MRRP-lab/ripple_robot/cad/fea/out/quasi-static_reaction_force.gif

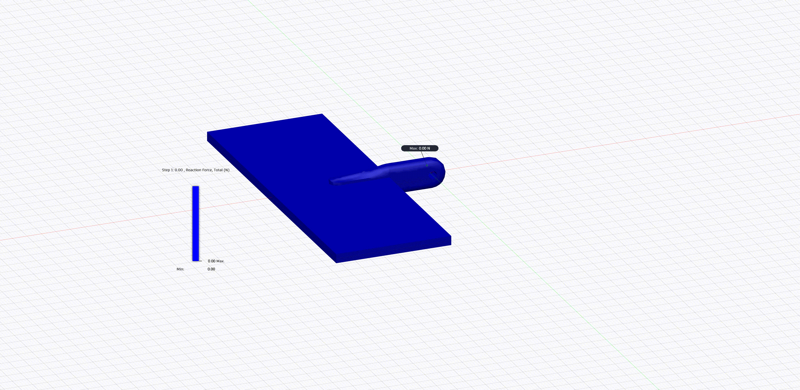
cad/fea/out/quasi-static_reaction_force.gif
