MRRP-lab/ripple_robot/cad/fea/out/quasi-static_stress.gif

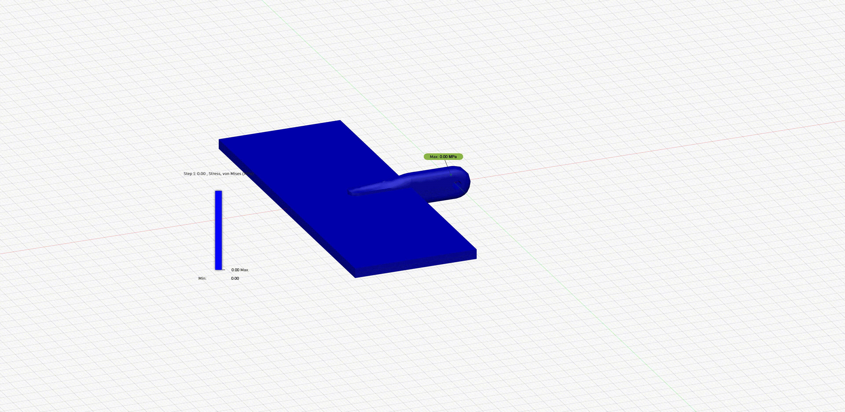
cad/fea/out/quasi-static_stress.gif
