MRRP-lab/ripple_robot/cad/fea/out/quasi-static_stress_cropped.gif

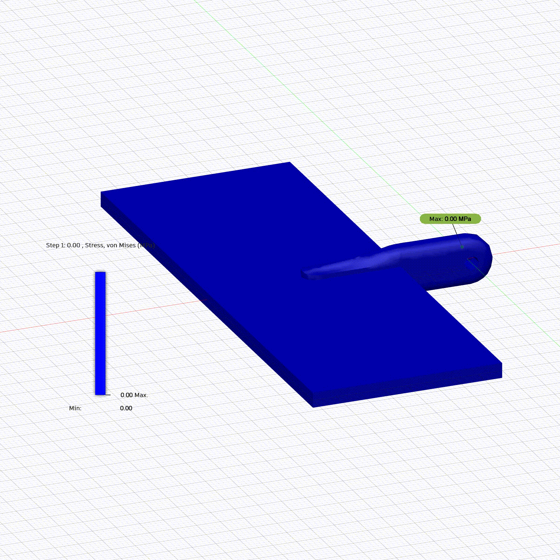
cad/fea/out/quasi-static_stress_cropped.gif
