MRRP-lab/ripple_robot/cad/fea/out/reaction_force_40deg.png

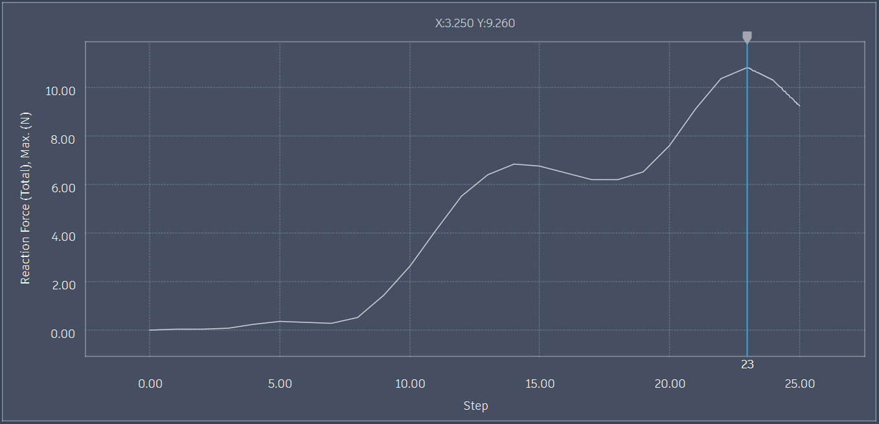
cad/fea/out/reaction_force_40deg.png
