MRRP-lab/ripple_robot/scripts/out/gait_stability.gif

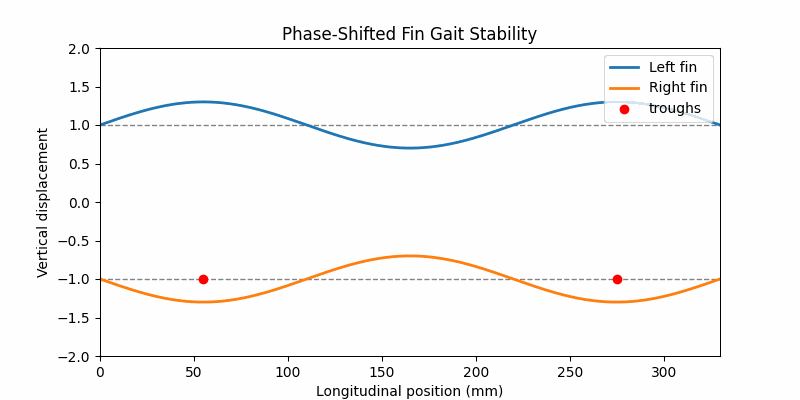
scripts/out/gait_stability.gif
