MRRP-lab/ripple_robot/cad/v4/stls/10p_passthrough_profile.stl

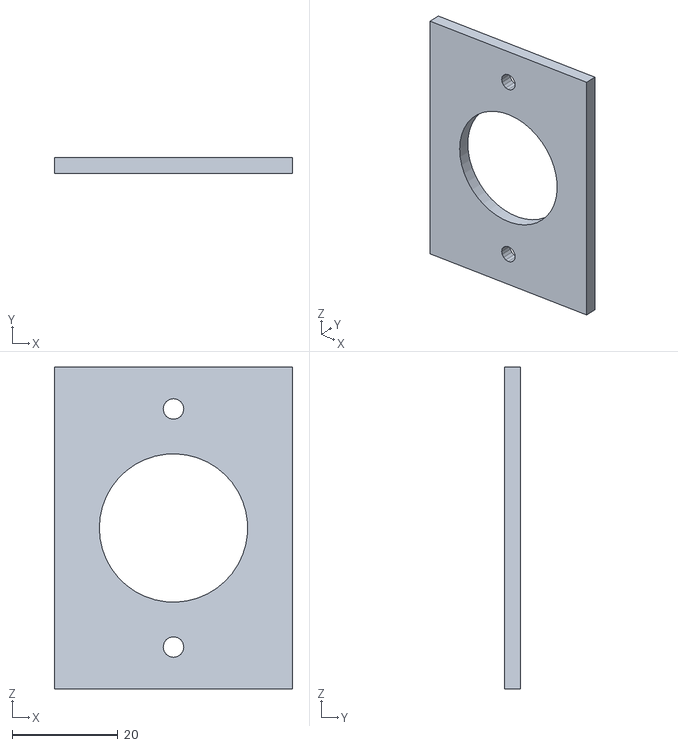
[picture p26: CAD file, 2026-06-12]
cad/v4/stls/10p_passthrough_profile.stl
45.1 x 3.00 x 61.0
