MRRP-lab/ripple_robot/cad/v4/stls/top_housing_cover.stl

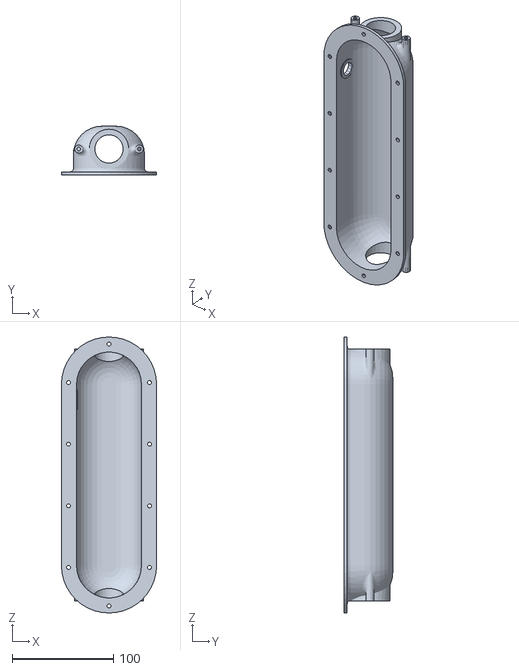
[picture p27: CAD file, 2026-06-12]
cad/v4/stls/top_housing_cover.stl
94.0 x 48.0 x 272.5
