MRRP-lab/ripple_robot/cad/v4/stls/top_housing_cover_v2.stl

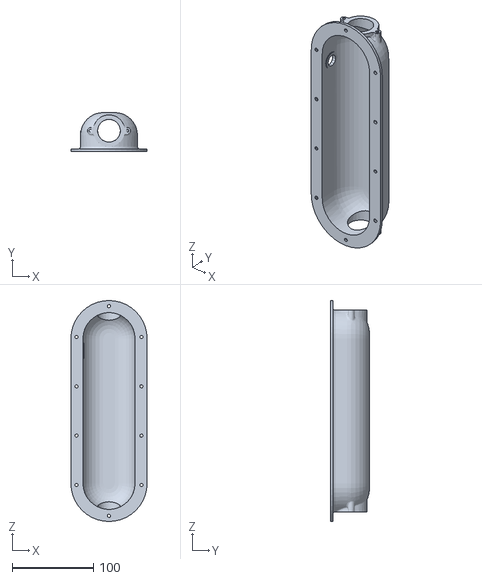
[picture p28: CAD file, 2026-06-12]
cad/v4/stls/top_housing_cover_v2.stl
94.0 x 48.0 x 272.5
