MRRP-lab/ripple_robot/cad/top_housing/stls/top_housing_screw_spacers.stl

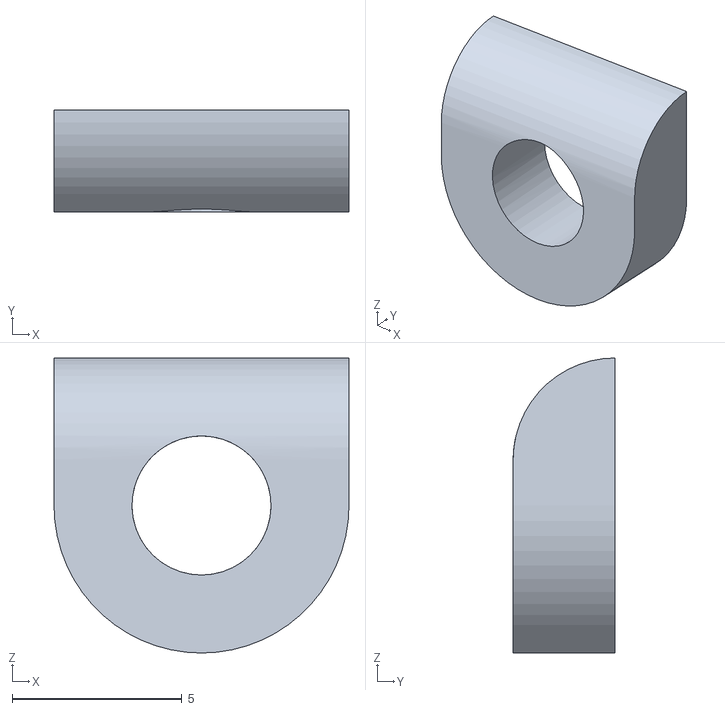
[picture p29: CAD file, 2026-06-12]
cad/top_housing/stls/top_housing_screw_spacers.stl
8.70 x 3.00 x 8.70
